onur-ulusoy/AUV-Acoustic-Processing-Board/Media/pictures/perspective-zoom.png

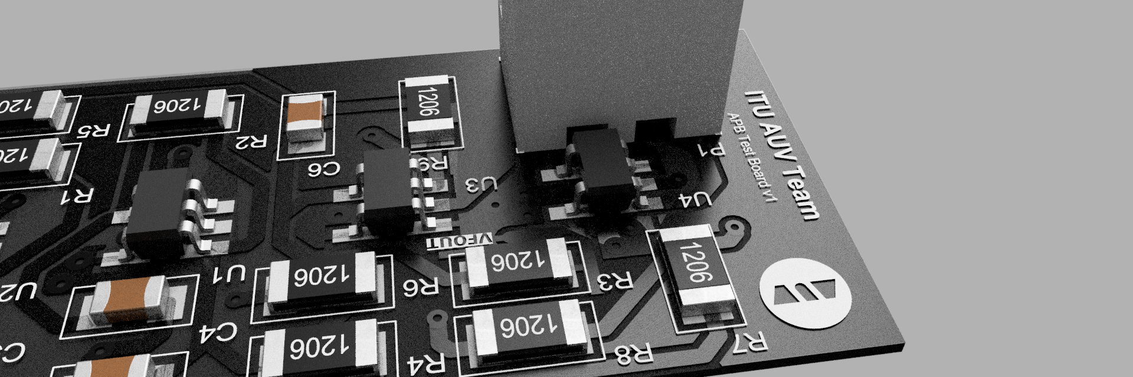
Media/pictures/perspective-zoom.png
