onur-ulusoy/AUV-Acoustic-Processing-Board/LTSpice_Simulation/APB_Filter.asc

C1: cap; 10µ
C2: cap; 10µ
C3: cap; 100n
C4: cap; 1n
C5: cap; 1n
C6: cap; 1n
C7: cap; 1n
C8: cap; 1n
C9: cap; 1n
C10: cap; 100n
C11: cap; 470p
C12: cap; 470p
C13: cap; 360p
C14: cap; 360p
C15: cap; 430p
C16: cap; 430p
C17: cap; 100n
C19: cap; 1n
C20: cap; 1n
C21: cap; 1n
C22: cap; 1n
C23: cap; 1n
C24: cap; 1n
J1: njf
J2: njf
J3: njf
R1: res; 1k
R2: res; 1k
R3: res; 1k
R4: res; 2k
R5: res; 10k
R6: res; 2k
R7: res; 62.2k
R8: res; 2k
R9: res; 15.38k
R10: res; 0.46k
R11: res; 46.23k
R12: res; 11.43k
R13: res; 0.34k
R14: res; 26.5k
R15: res; 13.26k
R16: res; 0.82k
R17: res; 1k
R18: res; 10k
R19: res; 2k
R20: res; 2k
R21: res; 57.6k
R22: res; 28.7k
R23: res; 1.74k
R24: res; 121k
R25: res; 62.2k
R26: res; 15.38k
R27: res; 0.46k
R28: res; 46.23k
R29: res; 11.43k
R30: res; 0.34k
R31: res; 26.5k
R32: res; 13.26k
R33: res; 0.82k
R34: res; 18.7k
R35: res; 845
R36: res; 165k
R37: res; 25.5k
R38: res; 1.18k
R39: res; 1k
R40: res; 10k
R41: res; 2k
R42: res; 2k
U1: AD8605
U2: AD8605
U3: AD8605
U4: AD8605
U5: AD8605
U6: AD8605
U7: AD8605
U8: AD8605
U9: AD8605
U10: AD8605
U11: AD8605
U12: AD8605
U13: AD8605
U14: AD8605
U15: AD8605
U16: AD8605
V1: voltage; SINE(3.3 0.1 20k 0.2m 0 0 10)
V2: voltage; SINE(0 0.5 35k 0.5m 0 0 10); AC 0.5
V4: voltage; SINE(0 0.5 35k 0.555m 0 0 10); AC 0.5
V6: voltage; SINE(0 0.5 36k 0.1m 0 0 10); AC 0.5
V8: voltage; 5
Named nets: VA, 0, AGND, VFIN, VAMPIN, VFOUT, VADC, VHYD-, VHYD+, VFIN2, VAMPIN2, VFOUT2, VHYD2-, VHYD2+, VFIN3, VAMPIN3, VFOUT3, VHYD3-, VHYD3+, VCC, VADC2, VADC3
.ac oct 100 10k 100k
Hydrophone Biasing
Analog Power Supply
Pre-Amplification
6 Pole Butterworth BandPass Filter
ADC Buffering
Hydrophone Biasing
Pre-Amplification
6 Pole Butterworth BandPass Filter
Hydrophone Biasing
Pre-Amplification
6 Pole Butterworth BandPass Filter
ADC Buffering
ADC Buffering
.ac oct 100 10k 100k
